shanalaufer/motor-monitor/receiver.py

import csv
import logging
import os
import socket
import json
import threading
from logging.handlers import RotatingFileHandler

import numpy as np
from scipy.fft import fft, fftfreq
import joblib
import pandas as pd
import requests

# ── Logging setup ────────────────────────────────────────────────────────────
_LOG_FORMAT = "%(asctime)s [%(levelname)s] %(message)s"
_formatter  = logging.Formatter(_LOG_FORMAT)

_console_handler = logging.StreamHandler()
_console_handler.setFormatter(_formatter)

_file_handler = RotatingFileHandler("receiver.log", maxBytes=1_000_000, backupCount=3)
_file_handler.setFormatter(_formatter)

log = logging.getLogger("receiver")
log.setLevel(logging.DEBUG)
log.addHandler(_console_handler)
log.addHandler(_file_handler)

# ── Config ───────────────────────────────────────────────────────────────────
LABEL = "healthy"  # "healthy" or "faulty"
API_URL = "https://motor-fault-api-f7r8.onrender.com"

model = joblib.load('motor_model.pkl')
fs = 500
burst_count = 0

# ── Quality stats ────────────────────────────────────────────────────────────
qc_total   = 0
qc_passed  = 0
qc_skipped = 0

EXPECTED_BURST_LEN = 256


def check_signal_quality(samples_x, samples_y, samples_z):
    """
    Run pre-pipeline signal quality checks on a 3-axis burst.
    Returns {"ok": True, "reason": None} on pass, or
            {"ok": False, "reason": "<description>"} on fail.
    """
    axes = {"x": samples_x, "y": samples_y, "z": samples_z}

    # 1. Empty or too-short burst
    for name, ax in axes.items():
        if len(ax) < 64:
            return {"ok": False, "reason": f"burst too short ({name}: {len(ax)} samples)"}

    # 2. Flat signal / sensor disconnect (std < 0.001 on ALL three axes)
    if all(np.std(ax) < 0.001 for ax in axes.values()):
        return {"ok": False, "reason": "flat signal — possible sensor disconnect"}

    # 3. Excessive noise (RMS > 20.0 on any axis)
    for name, ax in axes.items():
        rms = np.sqrt(np.mean(ax.astype(np.float64) ** 2))
        if rms > 20.0:
            return {"ok": False, "reason": f"excessive noise on {name} axis (RMS={rms:.2f})"}

    # 4. Clipping (more than 5% of samples at max or min value)
    for name, ax in axes.items():
        lo, hi = ax.min(), ax.max()
        clipped = np.sum((ax == lo) | (ax == hi))
        if clipped / len(ax) > 0.05:
            return {"ok": False, "reason": f"clipping on {name} axis ({clipped/len(ax)*100:.1f}% saturated)"}

    # 5. NaNs or Infs
    for name, ax in axes.items():
        if not np.all(np.isfinite(ax)):
            return {"ok": False, "reason": f"NaN or Inf values in {name} axis"}

    # 6. Sampling instability — burst length deviates > 10% from expected 256
    for name, ax in axes.items():
        deviation = abs(len(ax) - EXPECTED_BURST_LEN) / EXPECTED_BURST_LEN
        if deviation > 0.10:
            return {"ok": False, "reason": f"burst length instability ({name}: {len(ax)} vs expected {EXPECTED_BURST_LEN})"}

    return {"ok": True, "reason": None}


def extract_features(signal):
    signal = np.array(signal)
    signal = signal - np.mean(signal)
    rms = np.sqrt(np.mean(signal**2))
    peak = np.max(np.abs(signal))
    crest_factor = peak / rms
    N = len(signal)
    yf = np.abs(fft(signal)[:N//2]) * 2/N
    xf = fftfreq(N, 1/fs)[:N//2]
    def energy_at(hz, bw=5):
        mask = (xf >= hz - bw) & (xf <= hz + bw)
        return np.sum(yf[mask])
    return {
        'rms': float(rms),
        'peak': float(peak),
        'crest_factor': float(crest_factor),
        'energy_50hz': float(energy_at(50)),
        'energy_100hz': float(energy_at(100)),
        'energy_150hz': float(energy_at(150)),
    }

def _post_to_api(f):
    try:
        requests.post(f"{API_URL}/predict", json={'features': f}, timeout=5)
    except Exception as e:
        log.warning(f"API error: {e}")

server = socket.socket()
server.setsockopt(socket.SOL_SOCKET, socket.SO_REUSEADDR, 1)
server.bind(('0.0.0.0', 5001))
server.listen(5)
log.info(f"API URL: {API_URL}")
log.info("Listening for ESP32 on port 5001")
log.info(f"Expected burst length: {EXPECTED_BURST_LEN} samples")

while True:
    try:
        conn, addr = server.accept()
        data = b''
        conn.settimeout(5)
        try:
            while True:
                chunk = conn.recv(4096)
                if not chunk:
                    break
                data += chunk
        except:
            pass
        conn.close()
        current_label = 0
        if data:
            payload = json.loads(data.decode())

            # New 3-axis format; fall back to legacy single-axis key
            if 'samples_z' in payload:
                samples_x = np.array(payload['samples_x'], dtype=np.float32)
                samples_y = np.array(payload['samples_y'], dtype=np.float32)
                samples_z = np.array(payload['samples_z'], dtype=np.float32)
                pwm_duty  = payload.get('pwm_duty')
            else:
                samples_z = np.array(payload['samples'], dtype=np.float32)
                samples_x = samples_y = samples_z
                pwm_duty  = None

            # ── Signal quality check ─────────────────────────────────────────
            qc_total += 1
            qc = check_signal_quality(samples_x, samples_y, samples_z)
            if not qc["ok"]:
                qc_skipped += 1
                skip_rate = qc_skipped / qc_total * 100
                log.warning(f"QC SKIP — {qc['reason']} | passed={qc_passed} skipped={qc_skipped} skip_rate={skip_rate:.1f}%")
                continue
            qc_passed += 1
            skip_rate = qc_skipped / qc_total * 100

            features = extract_features(samples_z)  # Z axis drives existing pipeline
            features_df = pd.DataFrame([features])
            prediction = model.predict(features_df)[0]
            probability = model.predict_proba(features_df)[0][1]
            health_score = round((1 - probability) * 100, 1)
            status = "HEALTHY" if prediction == 0 else "FAULT DETECTED"
            log.info(
                f"Status: {status} | Health: {health_score}% | RMS: {features['rms']:.3f} "
                f"| CF: {features['crest_factor']:.3f} "
                f"| passed={qc_passed} skipped={qc_skipped} skip_rate={skip_rate:.1f}%"
            )

            threading.Thread(target=_post_to_api, args=(features,), daemon=True).start()

            # csv_path = 'real_data_v2.csv'
            # write_header = not os.path.exists(csv_path)
            # with open(csv_path, 'a', newline='') as f:
            #     writer = csv.writer(f)
            #     if write_header:
            #         writer.writerow(['rms', 'peak', 'crest_factor', 'energy_50hz', 'energy_100hz', 'energy_150hz', 'label'])
            #     writer.writerow([
            #         features['rms'],
            #         features['peak'],
            #         features['crest_factor'],
            #         features['energy_50hz'],
            #         features['energy_100hz'],
            #         features['energy_150hz'],
            #         current_label
            #     ])

            # npy_path = 'raw_healthy.npy' if LABEL == 'healthy' else 'raw_faulty.npy'
            # burst = np.stack([samples_x, samples_y, samples_z])  # shape (3, N)
            # if os.path.exists(npy_path):
            #     existing = np.load(npy_path)
            #     np.save(npy_path, np.concatenate([existing, burst[np.newaxis]], axis=0))
            # else:
            #     np.save(npy_path, burst[np.newaxis])  # shape (1, 3, N)

            burst_count += 1
            log.info(f"Burst {burst_count} saved ({LABEL})")

    except Exception as e:
        log.error(f"Main loop error: {e}")
